posssson/SmartSpin2k/include/BLE_Common.h

/*
 * Copyright (C) 2020  Anthony Doud & Joel Baranick
 * All rights reserved
 *
 * SPDX-License-Identifier: GPL-2.0-only
 */

#pragma once

// #define CONFIG_SW_COEXIST_ENABLE 1

#include <memory>
#include <NimBLEDevice.h>
#include <Arduino.h>
#include <Main.h>

// Heart Service
#define HEARTSERVICE_UUID        BLEUUID((uint16_t)0x180D)
#define HEARTCHARACTERISTIC_UUID BLEUUID((uint16_t)0x2A37)

// Cycling Power Service
#define CSCSERVICE_UUID              BLEUUID((uint16_t)0x1816)
#define CSCMEASUREMENT_UUID          BLEUUID((uint16_t)0x2A5B)
#define CYCLINGPOWERSERVICE_UUID     BLEUUID((uint16_t)0x1818)
#define CYCLINGPOWERMEASUREMENT_UUID BLEUUID((uint16_t)0x2A63)
#define CYCLINGPOWERFEATURE_UUID     BLEUUID((uint16_t)0x2A65)
#define SENSORLOCATION_UUID          BLEUUID((uint16_t)0x2A5D)

// Fitness Machine Service
#define FITNESSMACHINESERVICE_UUID              BLEUUID((uint16_t)0x1826)
#define FITNESSMACHINEFEATURE_UUID              BLEUUID((uint16_t)0x2ACC)
#define FITNESSMACHINECONTROLPOINT_UUID         BLEUUID((uint16_t)0x2AD9)
#define FITNESSMACHINESTATUS_UUID               BLEUUID((uint16_t)0x2ADA)
#define FITNESSMACHINEINDOORBIKEDATA_UUID       BLEUUID((uint16_t)0x2AD2)
#define FITNESSMACHINERESISTANCELEVELRANGE_UUID BLEUUID((uint16_t)0x2AD6)
#define FITNESSMACHINEPOWERRANGE_UUID           BLEUUID((uint16_t)0x2AD8)

// GATT service/characteristic UUIDs for Flywheel Bike from ptx2/gymnasticon/
#define FLYWHEEL_UART_SERVICE_UUID BLEUUID("6e400001-b5a3-f393-e0a9-e50e24dcca9e")
#define FLYWHEEL_UART_RX_UUID      BLEUUID("6e400002-b5a3-f393-e0a9-e50e24dcca9e")
#define FLYWHEEL_UART_TX_UUID      BLEUUID("6e400003-b5a3-f393-e0a9-e50e24dcca9e")
#define FLYWHEEL_BLE_NAME          "Flywheel 1"

// The Echelon Services
#define ECHELON_DEVICE_UUID  BLEUUID("0bf669f0-45f2-11e7-9598-0800200c9a66")
#define ECHELON_SERVICE_UUID BLEUUID("0bf669f1-45f2-11e7-9598-0800200c9a66")
#define ECHELON_WRITE_UUID   BLEUUID("0bf669f2-45f2-11e7-9598-0800200c9a66")
#define ECHELON_DATA_UUID    BLEUUID("0bf669f4-45f2-11e7-9598-0800200c9a66")

// macros to convert different types of bytes into int The naming here sucks and
// should be fixed.
#define bytes_to_s16(MSB, LSB) (((signed int)((signed char)MSB))) << 8 | (((signed char)LSB))
#define bytes_to_u16(MSB, LSB) (((signed int)((signed char)MSB))) << 8 | (((unsigned char)LSB))
#define bytes_to_int(MSB, LSB) ((static_cast<int>((unsigned char)MSB))) << 8 | (((unsigned char)LSB))
// Potentially, something like this is a better way of doing this ^^
// data.getUint16(1, true)

// Setup
void setupBLE();
extern TaskHandle_t BLECommunicationTask;
// ***********************Common**********************************
void BLECommunications(void *pvParameters);

// *****************************Server****************************
extern int bleConnDesc;  // These all need re
extern bool updateConnParametersFlag;

void startBLEServer();
void computeERG(int, int);
void computeCSC();
void updateIndoorBikeDataChar();
void updateCyclingPowerMesurementChar();
void calculateInstPwrFromHR();
void updateHeartRateMeasurementChar();
int connectedClientCount();

class MyServerCallbacks : public BLEServerCallbacks {
  void onConnect(BLEServer *, ble_gap_conn_desc *desc);
  void onDisconnect(BLEServer *);
};

class MyCallbacks : public BLECharacteristicCallbacks {
  void onWrite(BLECharacteristic *);
};

// *****************************Client*****************************

// Keeping the task outside the class so we don't need a mask.
// We're only going to run one anyway.
void bleClientTask(void *pvParameters);

// UUID's the client has methods for
// BLEUUID serviceUUIDs[4] = {FITNESSMACHINESERVICE_UUID,
// CYCLINGPOWERSERVICE_UUID, HEARTSERVICE_UUID, FLYWHEEL_UART_SERVICE_UUID};
// BLEUUID charUUIDs[4] = {FITNESSMACHINEINDOORBIKEDATA_UUID,
// CYCLINGPOWERMEASUREMENT_UUID, HEARTCHARACTERISTIC_UUID,
// FLYWHEEL_UART_TX_UUID};

class SpinBLEAdvertisedDevice {
 public:  // eventually these shoul be made private
  NimBLEAdvertisedDevice *advertisedDevice = nullptr;
  NimBLEAddress peerAddress;
  int connectedClientID = BLE_HS_CONN_HANDLE_NONE;
  BLEUUID serviceUUID   = (uint16_t)0x0000;
  BLEUUID charUUID      = (uint16_t)0x0000;
  bool userSelectedHR   = false;
  bool userSelectedPM   = false;
  bool userSelectedCSC  = false;
  bool userSelectedCT   = false;
  bool doConnect        = false;

  void set(BLEAdvertisedDevice *device, int id = BLE_HS_CONN_HANDLE_NONE, BLEUUID inserviceUUID = (uint16_t)0x0000, BLEUUID incharUUID = (uint16_t)0x0000) {
    advertisedDevice  = device;
    peerAddress       = device->getAddress();
    connectedClientID = id;
    serviceUUID       = BLEUUID(inserviceUUID);
    charUUID          = BLEUUID(incharUUID);
  }

  void reset() {
    advertisedDevice = nullptr;
    // NimBLEAddress peerAddress;
    connectedClientID = BLE_HS_CONN_HANDLE_NONE;
    serviceUUID       = (uint16_t)0x0000;
    charUUID          = (uint16_t)0x0000;
    userSelectedHR    = false;  // Heart Rate Monitor
    userSelectedPM    = false;  // Power Meter
    userSelectedCSC   = false;  // Cycling Speed/Cadence
    userSelectedCT    = false;  // Controllable Trainer
    doConnect         = false;  // Initiate connection flag
  }

  void print();
};

class SpinBLEClient {
 public:  // Not all of these need to be public. This should be cleaned up
          // later.
  boolean connectedPM        = false;
  boolean connectedHR        = false;
  boolean connectedCD        = false;
  boolean doScan             = false;
  bool intentionalDisconnect = false;
  int noReadingIn            = 0;
  int cscCumulativeCrankRev  = 0;
  int cscLastCrankEvtTime    = 0;

  BLERemoteCharacteristic *pRemoteCharacteristic = nullptr;

  // BLEDevices myBLEDevices;
  SpinBLEAdvertisedDevice myBLEDevices[NUM_BLE_DEVICES];

  void start();
  void serverScan(bool connectRequest);
  bool connectToServer();
  void scanProcess();
  void disconnect();
  // Check for duplicate services of BLEClient and remove the previoulsy
  // connected one.
  void removeDuplicates(NimBLEClient *pClient);
  // Reset devices in myBLEDevices[]. Bool All (true) or only connected ones
  // (false)
  void resetDevices();
  void postConnect(NimBLEClient *pClient);

 private:
  class MyAdvertisedDeviceCallback : public NimBLEAdvertisedDeviceCallbacks {
   public:
    void onResult(NimBLEAdvertisedDevice *);
  };

  class MyClientCallback : public NimBLEClientCallbacks {
   public:
    void onConnect(BLEClient *);
    void onDisconnect(BLEClient *);
    uint32_t onPassKeyRequest();
    bool onConfirmPIN(uint32_t);
    void onAuthenticationComplete(ble_gap_conn_desc);
  };
};

extern SpinBLEClient spinBLEClient;

struct FitnessMachineFeatureFlags {
  enum Types : uint {
    AverageSpeedSupported              = 1U << 0,
    CadenceSupported                   = 1U << 1,
    TotalDistanceSupported             = 1U << 2,
    InclinationSupported               = 1U << 3,
    ElevationGainSupported             = 1U << 4,
    PaceSupported                      = 1U << 5,
    StepCountSupported                 = 1U << 6,
    ResistanceLevelSupported           = 1U << 7,
    StrideCountSupported               = 1U << 8,
    ExpendedEnergySupported            = 1U << 9,
    HeartRateMeasurementSupported      = 1U << 10,
    MetabolicEquivalentSupported       = 1U << 11,
    ElapsedTimeSupported               = 1U << 12,
    RemainingTimeSupported             = 1U << 13,
    PowerMeasurementSupported          = 1U << 14,
    ForceOnBeltAndPowerOutputSupported = 1U << 15,
    UserDataRetentionSupported         = 1U << 16
  };
};

struct FitnessMachineTargetFlags {
  enum Types : uint {
    SpeedTargetSettingSupported                           = 1U << 0,
    InclinationTargetSettingSupported                     = 1U << 1,
    ResistanceTargetSettingSupported                      = 1U << 2,
    PowerTargetSettingSupported                           = 1U << 3,
    HeartRateTargetSettingSupported                       = 1U << 4,
    TargetedExpendedEnergyConfigurationSupported          = 1U << 5,
    TargetedStepNumberConfigurationSupported              = 1U << 6,
    TargetedStrideNumberConfigurationSupported            = 1U << 7,
    TargetedDistanceConfigurationSupported                = 1U << 8,
    TargetedTrainingTimeConfigurationSupported            = 1U << 9,
    TargetedTimeTwoHeartRateZonesConfigurationSupported   = 1U << 10,
    TargetedTimeThreeHeartRateZonesConfigurationSupported = 1U << 11,
    TargetedTimeFiveHeartRateZonesConfigurationSupported  = 1U << 12,
    IndoorBikeSimulationParametersSupported               = 1U << 13,
    WheelCircumferenceConfigurationSupported              = 1U << 14,
    SpinDownControlSupported                              = 1U << 15,
    TargetedCadenceConfigurationSupported                 = 1U << 16
  };
};

inline FitnessMachineFeatureFlags::Types operator|(FitnessMachineFeatureFlags::Types a, FitnessMachineFeatureFlags::Types b) {
  return static_cast<FitnessMachineFeatureFlags::Types>(static_cast<int>(a) | static_cast<int>(b));
}

inline FitnessMachineTargetFlags::Types operator|(FitnessMachineTargetFlags::Types a, FitnessMachineTargetFlags::Types b) {
  return static_cast<FitnessMachineTargetFlags::Types>(static_cast<int>(a) | static_cast<int>(b));
}

struct FitnessMachineFeature {
  union {
    struct {
      union {
        enum FitnessMachineFeatureFlags::Types featureFlags;
        uint8_t bytes[4];
      } featureFlags;
      union {
        enum FitnessMachineTargetFlags::Types targetFlags;
        uint8_t bytes[4];
      } targetFlags;
    };
    uint8_t bytes[8];
  };
};
