posssson/SmartSpin2k/src/BLE_Common.cpp

/*
 * Copyright (C) 2020  Anthony Doud & Joel Baranick
 * All rights reserved
 *
 * SPDX-License-Identifier: GPL-2.0-only
 */

#include "Main.h"
#include <math.h>
#include "BLE_Common.h"
#include "sensors/SensorData.h"
#include "sensors/SensorDataFactory.h"

int bleConnDesc               = 1;
bool updateConnParametersFlag = false;
TaskHandle_t BLECommunicationTask;
SensorDataFactory sensorDataFactory;

void BLECommunications(void *pvParameters) {
  for (;;) {
    // **********************************Client***************************************
    for (size_t x = 0; x < NUM_BLE_DEVICES; x++) {  // loop through discovered devices
      if (spinBLEClient.myBLEDevices[x].connectedClientID != BLE_HS_CONN_HANDLE_NONE) {
        // spinBLEClient.myBLEDevices[x].print();
        if (spinBLEClient.myBLEDevices[x].advertisedDevice) {  // is device registered?
          // debugDirector("1",false);
          SpinBLEAdvertisedDevice myAdvertisedDevice = spinBLEClient.myBLEDevices[x];
          if ((myAdvertisedDevice.connectedClientID != BLE_HS_CONN_HANDLE_NONE) && (myAdvertisedDevice.doConnect == false)) {  // client must not be in connection process
            // debugDirector("2",false);
            if (BLEDevice::getClientByPeerAddress(myAdvertisedDevice.peerAddress)) {  // nullptr check
              // debugDirector("3",false);
              BLEClient *pClient = NimBLEDevice::getClientByPeerAddress(myAdvertisedDevice.peerAddress);
              // Client connected with a valid UUID registered
              if ((myAdvertisedDevice.serviceUUID != BLEUUID((uint16_t)0x0000)) && (pClient->isConnected())) {
                // debugDirector("4");
                // Write the recieved data to the Debug Director

                BLERemoteCharacteristic *pRemoteBLECharacteristic = pClient->getService(myAdvertisedDevice.serviceUUID)->getCharacteristic(myAdvertisedDevice.charUUID);
                std::string data                                  = pRemoteBLECharacteristic->getValue();
                uint8_t *pData                                    = reinterpret_cast<uint8_t *>(&data[0]);
                int length                                        = data.length();

                // 250 == Data(60), Spaces(Data/2), Arrow(4), SvrUUID(37), Sep(3), ChrUUID(37), Sep(3),
                //        Name(10), Prefix(2), HR(8), SEP(1), CD(10), SEP(1), PW(8), SEP(1), SP(7), Suffix(2), Nul(1) - 225 rounded up
                char logBuf[250];
                char *logBufP = logBuf;
                for (int i = 0; i < length; i++) {
                  logBufP += sprintf(logBufP, "%02x ", pData[i]);
                }
                logBufP += sprintf(logBufP, "<- %.8s | %.8s", myAdvertisedDevice.serviceUUID.toString().c_str(), myAdvertisedDevice.charUUID.toString().c_str());

                std::shared_ptr<SensorData> sensorData = sensorDataFactory.getSensorData(pRemoteBLECharacteristic, pData, length);

                logBufP += sprintf(logBufP, " | %s:[", sensorData->getId().c_str());
                if (sensorData->hasHeartRate()) {
                  int heartRate = sensorData->getHeartRate();
                  userConfig.setSimulatedHr(heartRate);
                  spinBLEClient.connectedHR |= true;
                  logBufP += sprintf(logBufP, " HR(%d)", heartRate % 1000);
                }
                if (sensorData->hasCadence()) {
                  float cadence = sensorData->getCadence();
                  userConfig.setSimulatedCad(cadence);
                  spinBLEClient.connectedCD |= true;
                  logBufP += sprintf(logBufP, " CD(%.2f)", fmodf(cadence, 1000.0));
                }
                if (sensorData->hasPower()) {
                  int power = sensorData->getPower();
                  if (userConfig.getDoublePower()) {
                    userConfig.setSimulatedWatts(power * 2);
                  } else {
                    userConfig.setSimulatedWatts(power);
                  }
                  spinBLEClient.connectedPM |= true;
                  logBufP += sprintf(logBufP, " PW(%d)", power % 10000);
                }
                if (sensorData->hasSpeed()) {
                  float speed = sensorData->getSpeed();
                  userConfig.setSimulatedSpeed(speed);
                  logBufP += sprintf(logBufP, " SD(%.2f)", fmodf(speed, 1000.0));
                }
                strcat(logBufP, " ]");
                debugDirector(String(logBuf), true, true);
              } else if (!pClient->isConnected()) {  // This shouldn't ever be
                                                     // called...
                if (pClient->disconnect() == 0) {    // 0 is a successful disconnect
                  BLEDevice::deleteClient(pClient);
                  vTaskDelay(100 / portTICK_PERIOD_MS);
                  debugDirector("Workaround connect");
                  myAdvertisedDevice.doConnect = true;
                }
              }
            }
          }
        }
      }
    }

    // ***********************************SERVER**************************************
    if ((spinBLEClient.connectedHR && !spinBLEClient.connectedPM) && (userConfig.getSimulatedHr() > 0) && userPWC.hr2Pwr) {
      calculateInstPwrFromHR();
    }
#ifdef DEBUG_HR_TO_PWR
    calculateInstPwrFromHR();
#endif

    if (!spinBLEClient.connectedPM && !userPWC.hr2Pwr) {
      userConfig.setSimulatedCad(0);
      userConfig.setSimulatedWatts(0);
    }
    if (!spinBLEClient.connectedHR) {
      userConfig.setSimulatedHr(0);
    }

    if (connectedClientCount() > 0) {
      // update the BLE information on the server
      computeCSC();
      updateIndoorBikeDataChar();
      updateCyclingPowerMesurementChar();
      updateHeartRateMeasurementChar();

      if (updateConnParametersFlag) {
        vTaskDelay(100 / portTICK_PERIOD_MS);
        // BLEDevice::getServer()->updateConnParams(bleConnDesc, 40, 50,
        // 0, 100);
        BLEDevice::getServer()->updateConnParams(bleConnDesc, 80, 200, 0, 800);
        updateConnParametersFlag = false;
      }
    } else {
    }
    if (connectedClientCount() == 0) {
      digitalWrite(LED_PIN, LOW);  // blink if no client connected
    }
    if (BLEDevice::getAdvertising()) {
      if (!(BLEDevice::getAdvertising()->isAdvertising()) && (BLEDevice::getServer()->getConnectedCount() < CONFIG_BT_NIMBLE_MAX_CONNECTIONS - NUM_BLE_DEVICES)) {
        debugDirector("Starting Advertising From Communication Loop");
        BLEDevice::startAdvertising();
      }
    }

    vTaskDelay((BLE_NOTIFY_DELAY / 2) / portTICK_PERIOD_MS);
    digitalWrite(LED_PIN, HIGH);
    vTaskDelay((BLE_NOTIFY_DELAY / 2) / portTICK_PERIOD_MS);
#ifdef DEBUG_STACK
    Serial.printf("BLEComm: %d \n", uxTaskGetStackHighWaterMark(BLECommunicationTask));
#endif
  }
}
