posssson/SmartSpin2k/include/HTTP_Server_Basic.h

/*
 * Copyright (C) 2020  Anthony Doud & Joel Baranick
 * All rights reserved
 *
 * SPDX-License-Identifier: GPL-2.0-only
 */

#pragma once

#include <Arduino.h>

void startHttpServer();
void webClientUpdate(void *pvParameters);
void handleSpiffsFile();
void handleIndexFile();
void settingsProcessor();
void handleHrSlider();
void FirmwareUpdate();

#ifdef USE_TELEGRAM
void sendTelegram(String textToSend);
void telegramUpdate(void *pvParameters);
#endif

// wifi Function
void startWifi();
